felixmark/Omamori/0.3/Images/Front_back.png

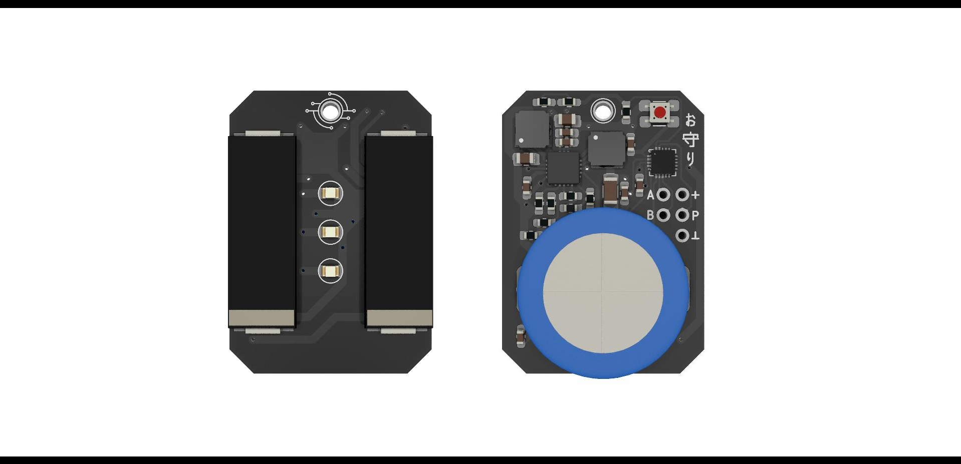
0.3/Images/Front_back.png
