felixmark/Omamori/0.3/Images/Omamori2.jpg

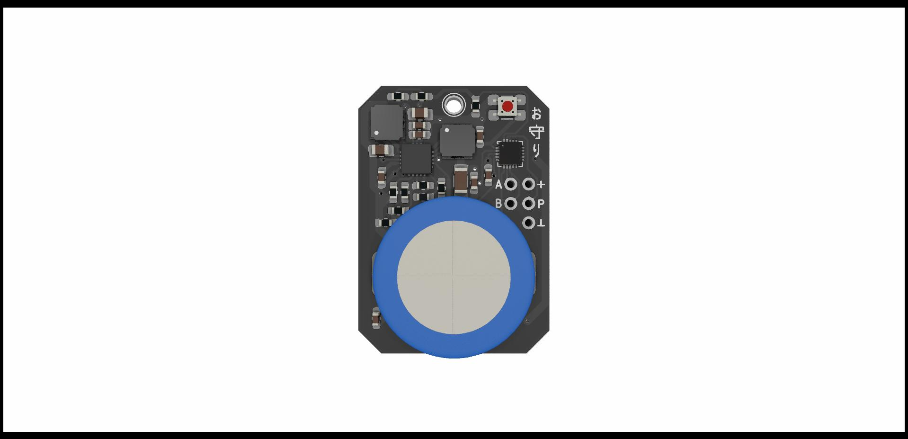
0.3/Images/Omamori2.jpg
