felixmark/Omamori/0.3/Images/photo_back.jpg

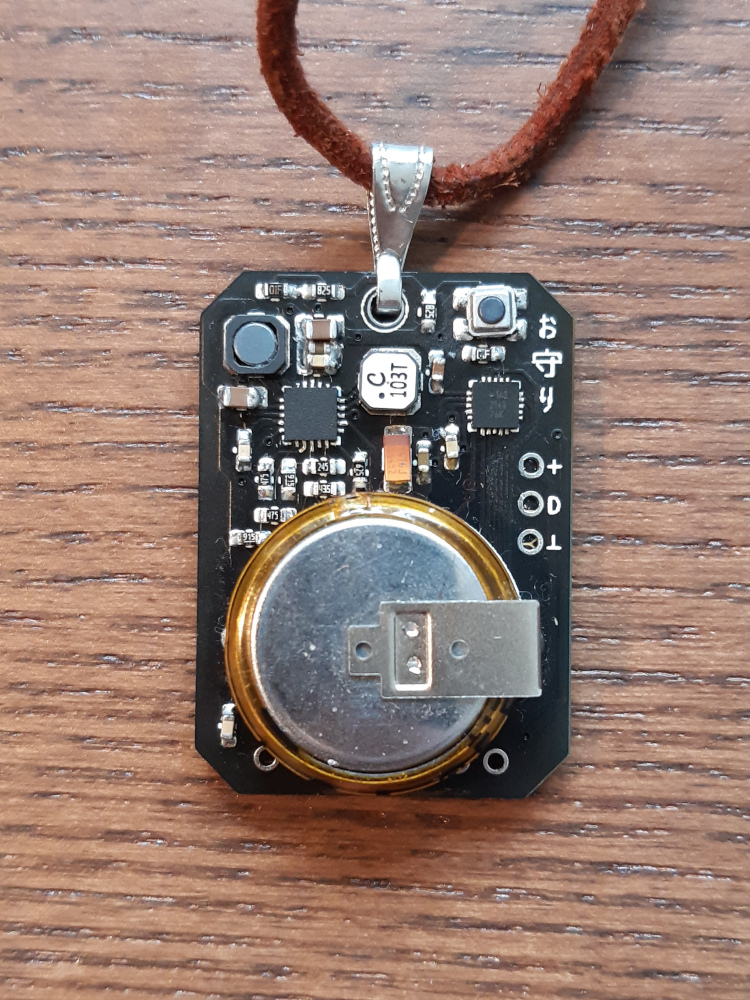
0.3/Images/photo_back.jpg
