felixmark/Omamori/Datasheets/ATtiny_x26.png

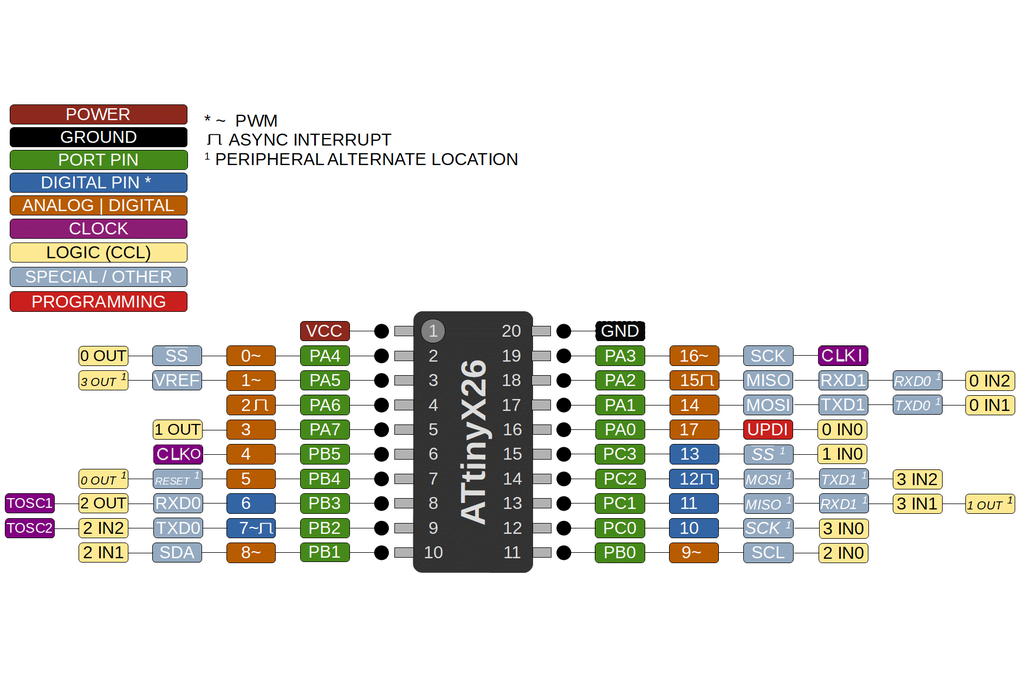
Datasheets/ATtiny_x26.png
