felixmark/Omamori/Datasheets/Resistors.png

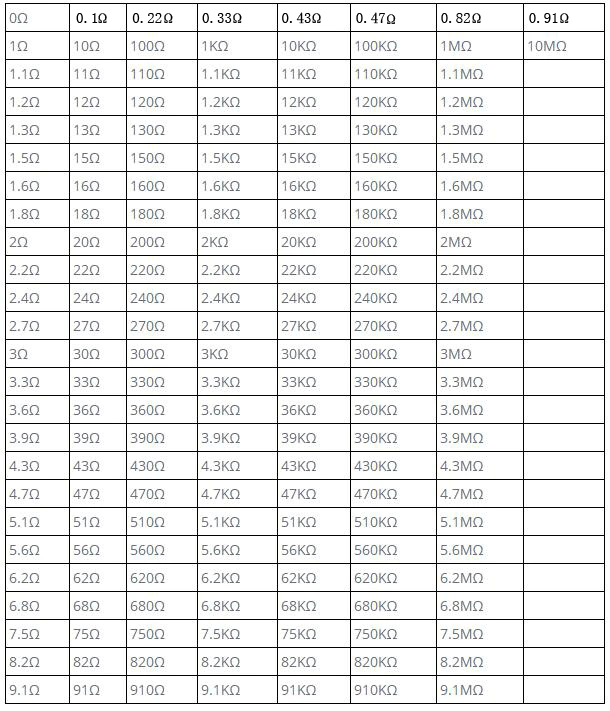
Datasheets/Resistors.png
