felixmark/Omamori/general/Images/Omamori_Pixelart.png

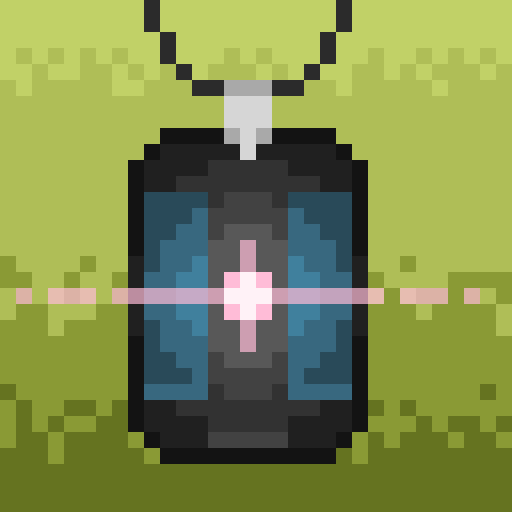
general/Images/Omamori_Pixelart.png
