felixmark/Omamori/0.2/Images/solder_guide_0.2.1.png

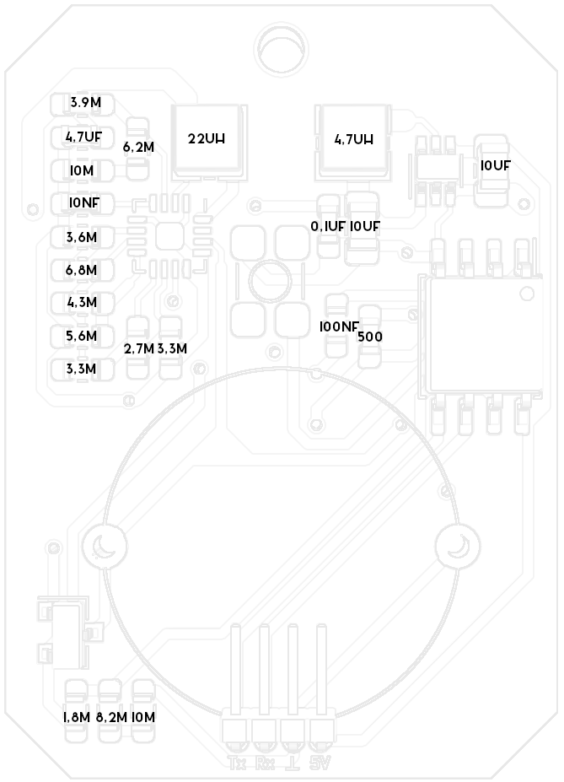
0.2/Images/solder_guide_0.2.1.png
